PastaLaPate/DIY_MovingHeadLight/include/ServerUtils.h

#include <SETTINGS.h>

#include <ArduinoJson.h>
#include <ESPAsyncWebServer.h>
#include <ElegantOTA.h> // Can get free pro version w/ https://github.com/Missing-Link-harkat/ESP32-Scanner-POE/blob/main/lib/ElegantOTAPro/ElegantOTAPro.h

void setupServer();
void loopServer();
